ZouhirYachou/Z4_E85_E86_retrofit_Alpine_i905D-F/images/PXL_20240806_155523220.jpg

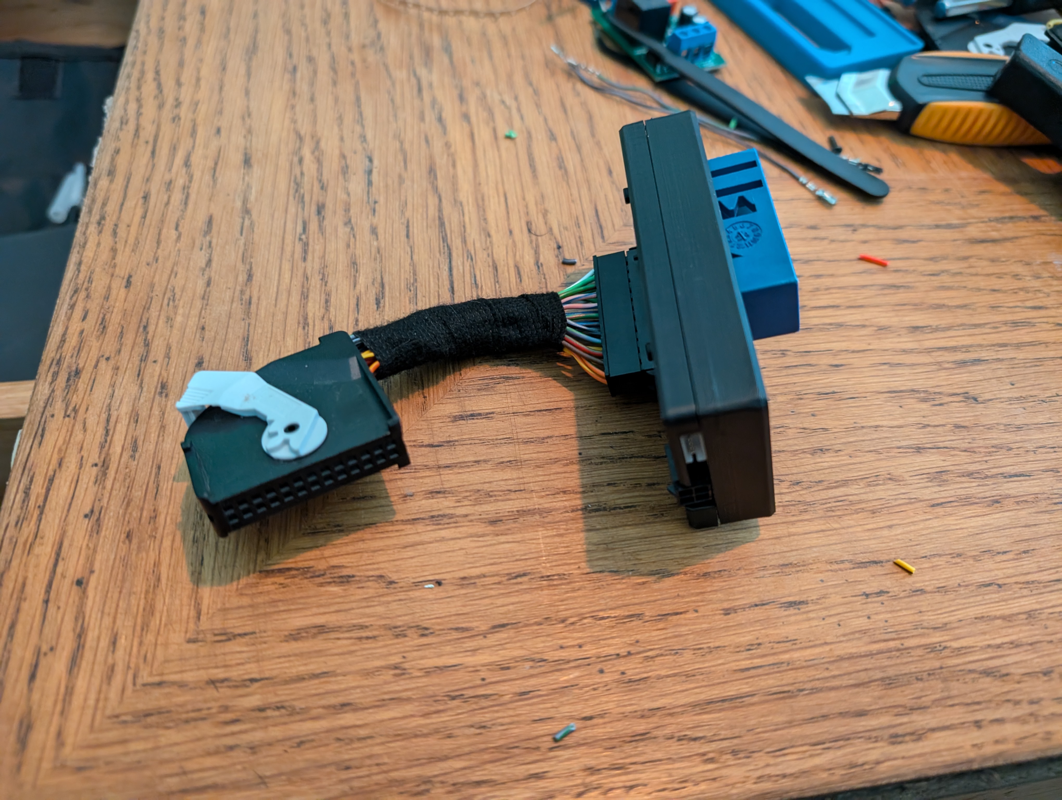
images/PXL_20240806_155523220.jpg
