ZouhirYachou/Z4_E85_E86_retrofit_Alpine_i905D-F/images/PXL_20240822_180815933.jpg

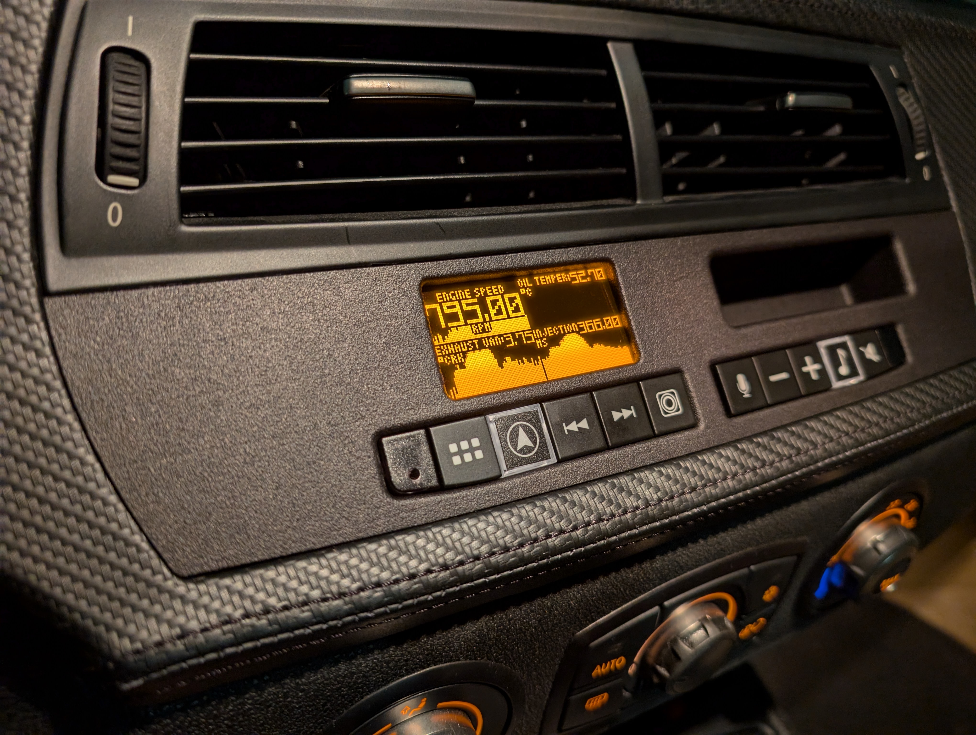
images/PXL_20240822_180815933.jpg
